ostat/vacuum-hose-adapter-openscad/samples/bosch_sander_sample.png

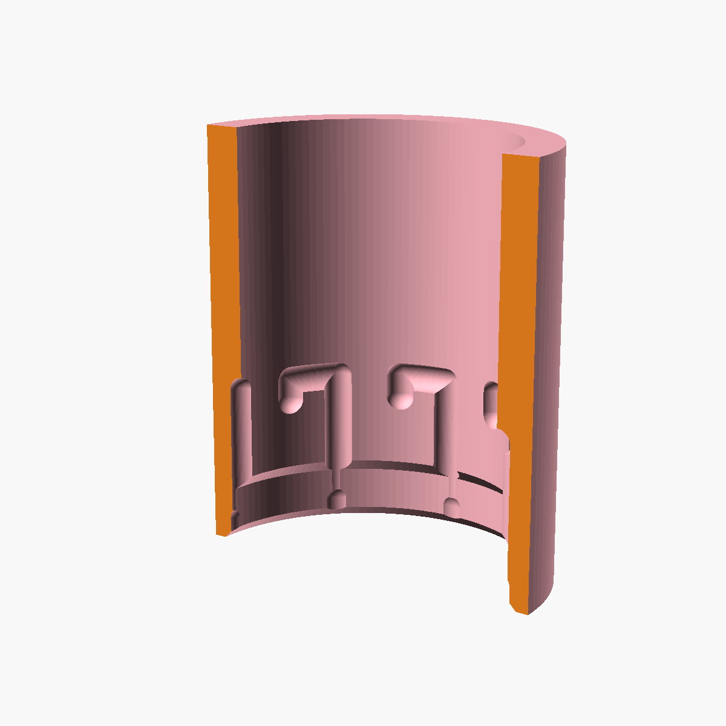
samples/bosch_sander_sample.png
