ostat/vacuum-hose-adapter-openscad/samples/100mm_magnet_flange_to_50mm_hose.stl

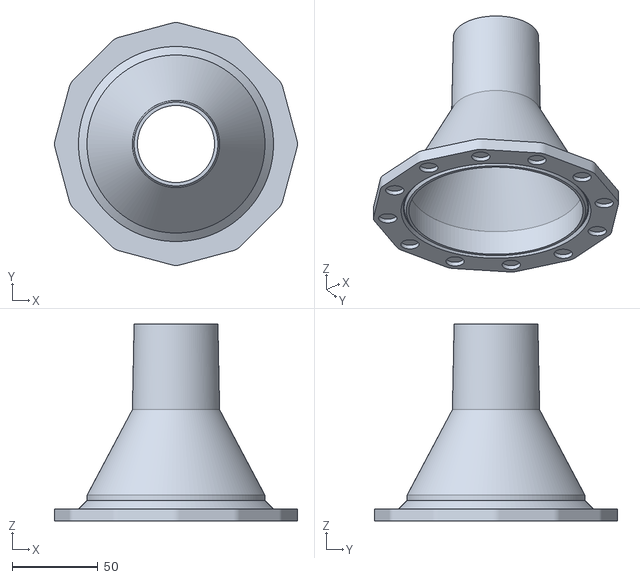
[picture p28: CAD file, 2022-09-24]
samples/100mm_magnet_flange_to_50mm_hose.stl
142.0 x 142.0 x 115.0
