ostat/vacuum-hose-adapter-openscad/samples/50mm_hose_to_30mm_hose.stl

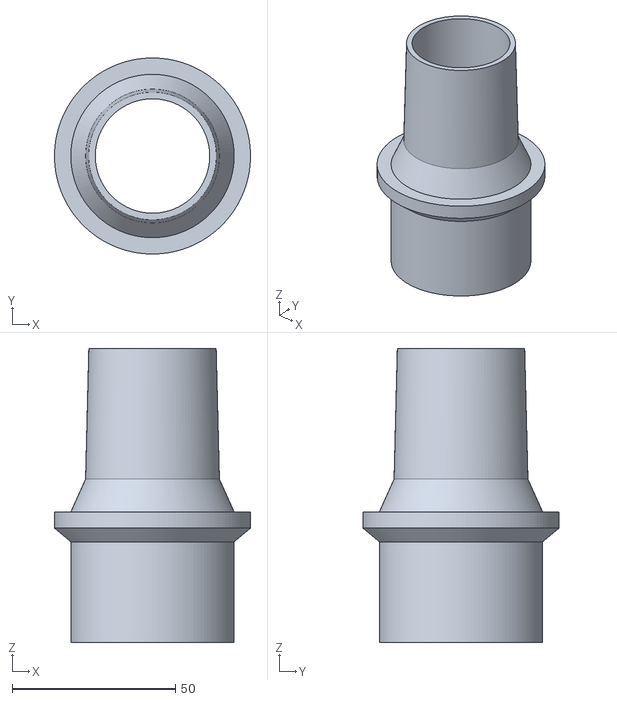
[picture p29: CAD file, 2022-09-24]
samples/50mm_hose_to_30mm_hose.stl
60.0 x 60.0 x 90.0
