ostat/vacuum-hose-adapter-openscad/samples/flat_plate_to_50mm_hose.stl

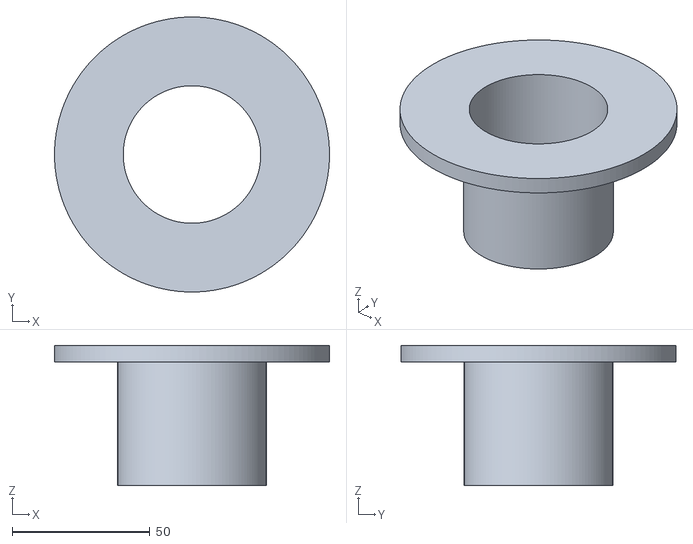
[picture p30: CAD file, 2022-09-24]
samples/flat_plate_to_50mm_hose.stl
100.0 x 100.0 x 51.0
