ostat/vacuum-hose-adapter-openscad/samples/50mm_magnet_to_100mm_magnet.stl

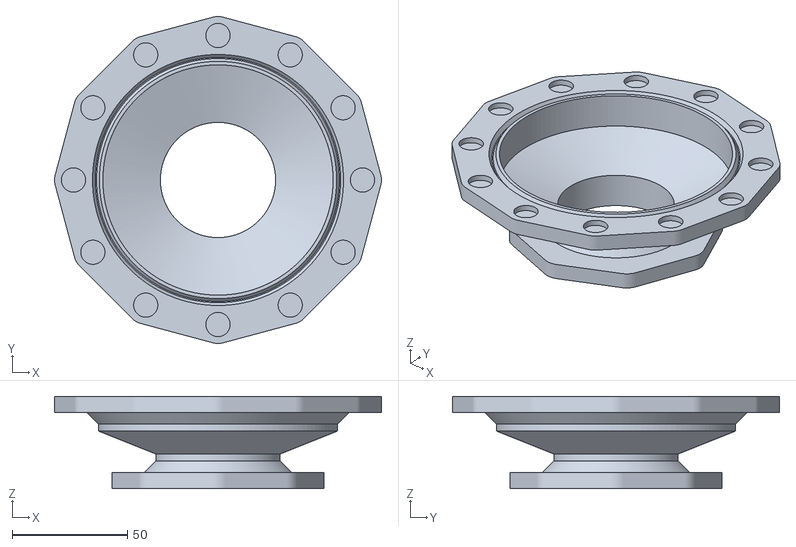
[picture p31: CAD file, 2022-09-24]
samples/50mm_magnet_to_100mm_magnet.stl
142.0 x 142.0 x 40.0
