ostat/vacuum-hose-adapter-openscad/samples/50mm_magnet_to_flat_plate_with_connector.stl

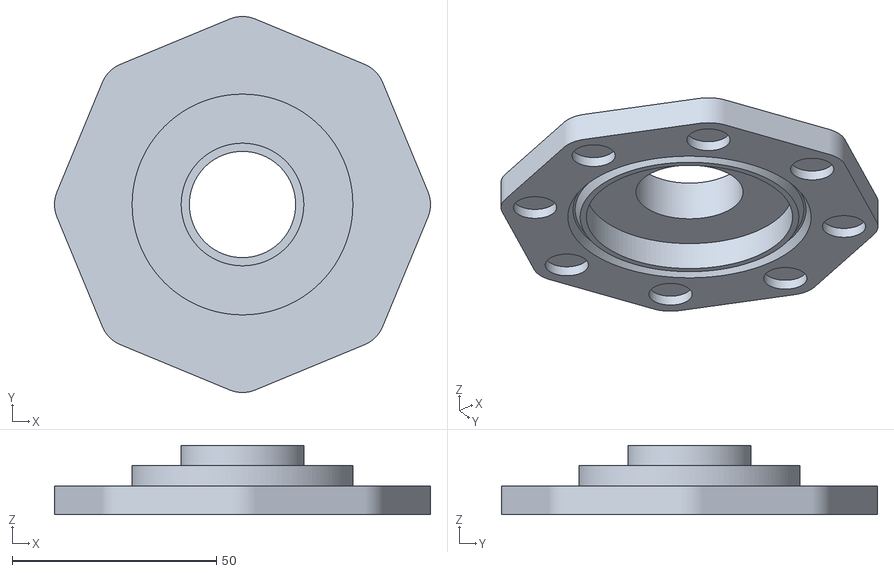
[picture p32: CAD file, 2022-09-24]
samples/50mm_magnet_to_flat_plate_with_connector.stl
92.0 x 92.0 x 17.0
