ostat/vacuum-hose-adapter-openscad/samples/50mm_hose_to_100mm_hose.stl

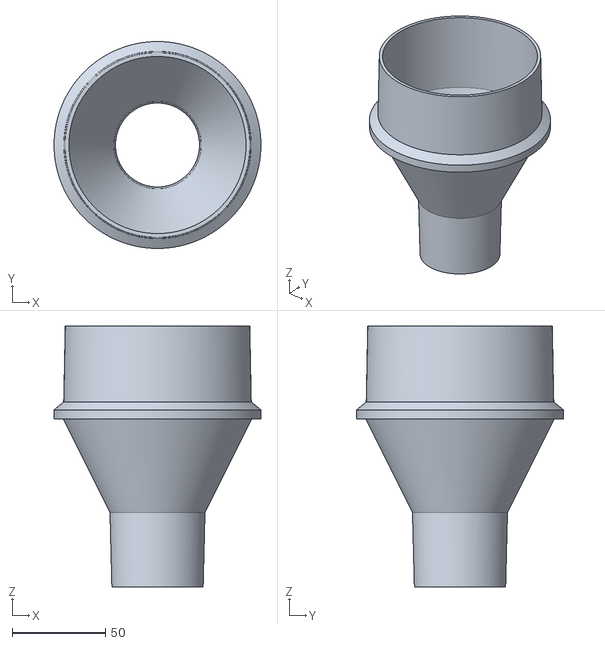
[picture p34: CAD file, 2022-09-24]
samples/50mm_hose_to_100mm_hose.stl
111.0 x 111.0 x 140.0
