ostat/vacuum-hose-adapter-openscad/samples/50m_magnet_flange_alignment_ring.stl

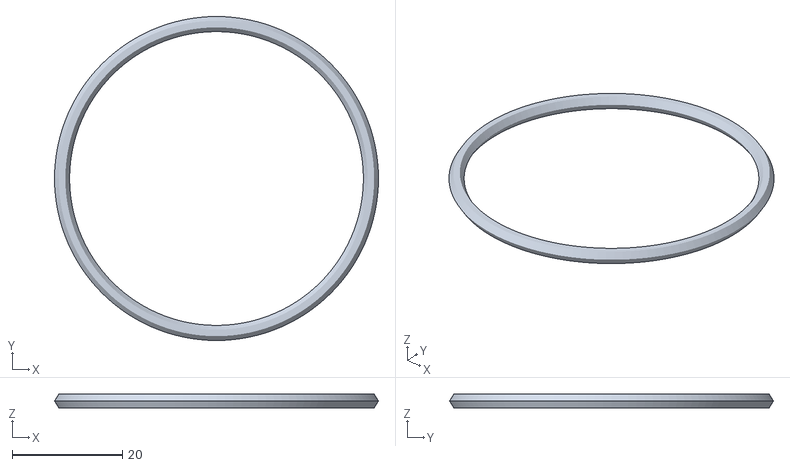
[picture p35: CAD file, 2022-09-24]
samples/50m_magnet_flange_alignment_ring.stl
58.8 x 58.8 x 2.50
