ostat/vacuum-hose-adapter-openscad/samples/100mm_magnet_flange_alignment_ring.stl

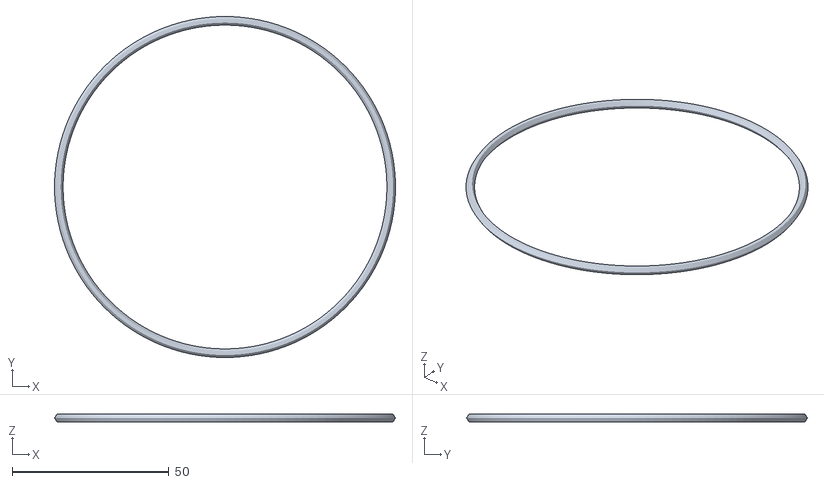
[picture p36: CAD file, 2022-09-24]
samples/100mm_magnet_flange_alignment_ring.stl
108.8 x 108.8 x 2.50
