ostat/vacuum-hose-adapter-openscad/samples/50mm_magnet_to_100mm.stl

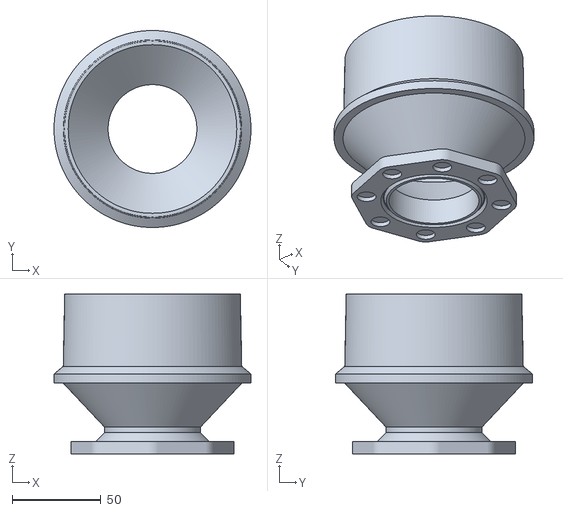
[picture p37: CAD file, 2022-09-24]
samples/50mm_magnet_to_100mm.stl
111.0 x 111.0 x 90.0
