ostat/vacuum-hose-adapter-openscad/samples/50mm_magnet_to_40mm.stl

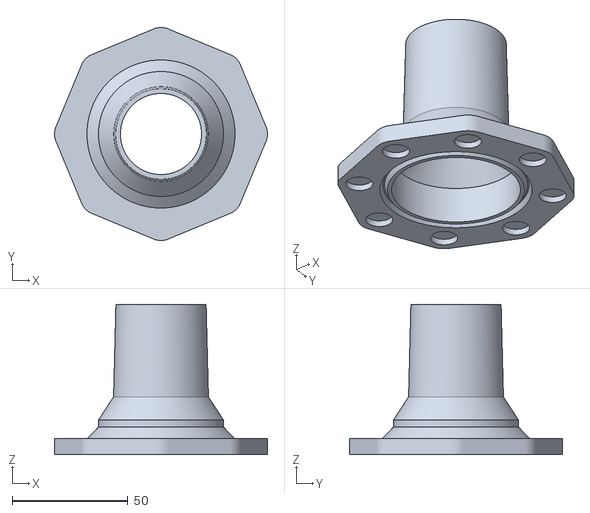
[picture p38: CAD file, 2022-09-24]
samples/50mm_magnet_to_40mm.stl
92.0 x 92.0 x 65.0
