ostat/vacuum-hose-adapter-openscad/modules/connector_camlock.scad

include <constants.scad>

camlockVersion = "1.0";
camlockMinLength = 35+3;
camlockMeasurement = "outer";
camlockOuterDiameter = 24.25*2;

camlockSettings = ["camlock", [
  [iSettingsLength, camlockMinLength],
  [iSettingsMeasurement, camlockMeasurement],
  [iSettingsDiameter, camlockOuterDiameter],
  [iSettingsTaper ,0],
  [iSettingsVersion, camlockVersion]
  ]];

 /*
 CamlockConnector(
  innerEndDiameter = camlockOuterDiameter,
  length = camlockMinLength,
  wallThickness = 2);
 */

module CamlockConnector(
  innerEndDiameter,
  length,
  wallThickness){

  innerDiameter =  20*2;
  //camlockOuterDiameter = 48.5;
  outerDiameter = camlockOuterDiameter;
  camlockHeight = 35;
  camlockStopLength = camlockMinLength - camlockHeight;
  camlockStopWidth = camlockStopLength/2.1;
  camlockWallThickness = (outerDiameter - innerDiameter)/2;
  camlockRingClipRadius = 5.1;//4.8;
  camlockRingClipHeight = 15;
  camlockRingClipPosition = 27.25;
  camlockChamfer = 1.6;
  camlockChamferLength = 1.6;

 echo("CamlockConnector", innerDiameter = innerDiameter, outerDiameter=outerDiameter, camlockHeight=camlockHeight, length = length, camlockWallThickness = camlockWallThickness);

  difference(){
    HoseConnector(
      connectorMeasurement = "outer",
      innerStartDiameter = innerDiameter,
      innerEndDiameter = innerDiameter,
      length = camlockHeight,
      wallThickness = camlockWallThickness,
      stopLength = camlockStopLength,
      stopWidth = camlockStopWidth,
      stopSymmetrical = 0,
      chamferLength = camlockChamferLength,
      chamferWidth= camlockChamfer
    );

    //hollow out top to reduce width and plastic, and match desired width
    translate([0,0,camlockRingClipHeight+wallThickness/2])
    HoseConnector(
      connectorMeasurement = "outer",
      innerStartDiameter = innerDiameter-wallThickness*2,
      innerEndDiameter = innerDiameter-wallThickness*2,
      length = camlockHeight+camlockStopLength+fudgeFactor*2-(camlockRingClipHeight+wallThickness/2),
      wallThickness = camlockWallThickness,
      stopLength = 0,
      stopWidth = 0,
      stopSymmetrical = 0,
      chamferLength = camlockWallThickness,
      chamferWidth= camlockWallThickness
    );

    //subtract the ring lock
    translate([0,0,camlockRingClipHeight])
      rotate_extrude(angle = 360, convexity = 2)
      translate([camlockRingClipPosition,0,0])
      circle(camlockRingClipRadius);
  }

  /*Pipe (
    diameter1 = innerDiameter,
    diameter2 = innerEndDiameter,
    length = length - camlockHeight,
    wallThickness1 = (outerDiameter - innerDiameter)/2,
    wallThickness2 = wallThickness,
    zPosition = camlockHeight);*/
}
