ostat/vacuum-hose-adapter-openscad/modules/functions_general.scad

include <functions_custom_config.scad>
include <functions_dictionary.scad>
include <functions_array.scad>

/*
U+1F7E5 🟥 LARGE RED SQUARE
U+1F7E6 🟦 LARGE BLUE SQUARE
U+1F7E7 🟧 LARGE ORANGE SQUARE
U+1F7E8 🟨 LARGE YELLOW SQUARE
U+1F7E9 🟩 LARGE GREEN SQUARE
U+1F7EA 🟪 LARGE PURPLE SQUARE
U+1F7EB 🟫 LARGE BROWN SQUARE
U+2B1B ⬛ BLACK LARGE SQUARE
U+2B1C ⬜ WHITE LARGE SQUARE
*/
